maheshwari-aniruddh/weathergotchi/bom/xiao-esp32c6.png

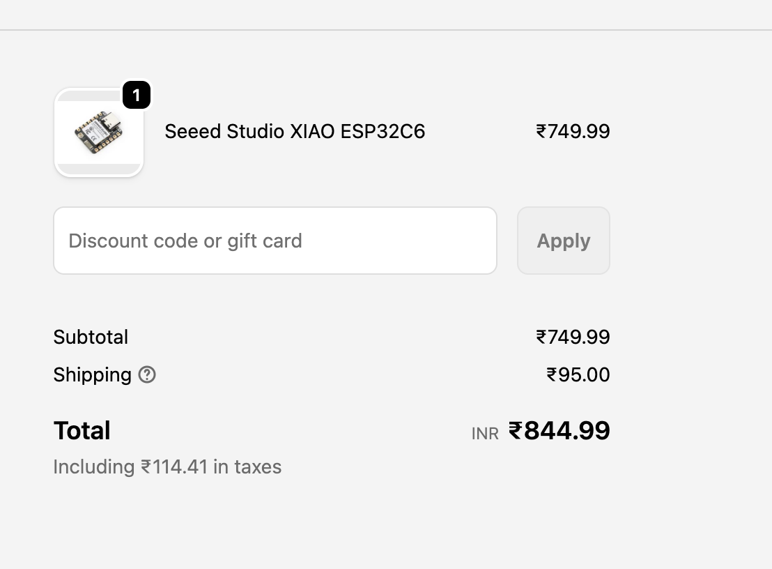
bom/xiao-esp32c6.png
